ChayaninNapia/IoT_SmartWatt_Meter/proposal/G03_ใบเปิดโครงการ.pdf

โครงงานศึกษา Class Project สถาบันวิทยาการหุ่นยนต์ภาคสนาม (ฟีโบ้) มหาวิทยาลัยเทคโนโลยีพระจอมเกล้าธนบุรี ประจําปีการศึกษา 2/2569

วิชาเรียน
วิชา FRA 163 สตูดิโอวิทยาการหุ่นยนต์ 1 : ขับเคลื่อนด้วยวิทยาศาสตร์ (Robotics Studio I : Science in Motion) ชื่อโครงงาน
เครื่องยิงลูกสควอสแบบปริงกด

ผู้รับผิดชอบโครงงาน
นักศึกษาระดับปริญญาตรี ชั้นปีที่ 1 (รหัส 68) จํานวน 6 คน กลุ่มที่ 3
1. นายชวัลกร | ฐานพงศ์พันธุ์ | รหัสนักศึกษา 68340500016
2. นายโชติพิสุทธิ์ มงคลวิสุทธิ์ | รหัสนักศึกษา 68340500020
3. นางสาวพีรยา กันสิงห์ | รหัสนักศึกษา 68340500042
4. นายพีรวิชญ์ | ศิริเศรษฐ์ | รหัสนักศึกษา 68340500043
5. นายจิรวัฒน์ | ดอนโบราณ | รหัสนักศึกษา 68340500060
6. นายมณฑล | จวงสันเทียะ | รหัสนักศึกษา 68340500078

อาจารย์ที่ปรึกษากลุ่ม
1. ผศ.ดร.เอกชัย เป็งวัง
2. ดร.รัตนชัย รมัยธิติมา
3. ดร.บุญฑริกา เกษมสันติธรรม
4. ดร.ปิติวุฒญ์ ธีรกิตติกุล
5. ดร.วุฒิพงษ์ ปรีชาพลกุล
6. นายพุฒินาท อาชีวะวานิช
บทนํา
เครื่องยิงลูกสควอชที่ใช้กลไกสปริงกดในการส่งกําลังและยิงลูกสควอชออกไปตกในเป้าหมายที่กําหนดไว้ โดยหลักการ ทํางานของเครื่องคือการใช้ Linear Guide เคลื่อนที่เพื่อให้Solenoid Lock เข้าหากัน และใช้ Lead Screw ในการดึงให้ Solenoid Lock ลงมาจนถึงระยะที่กําหนดไว้ ทําการหน่วงเวลาด้วยวงจรไฟฟ้า Timer Circuit เมื่อถึงเวลาที่กําหนดไว้Solenoid Lock จะปล่อยออกจากกัน จึงทําให้ลูกสควอชถูกยิงออกไป

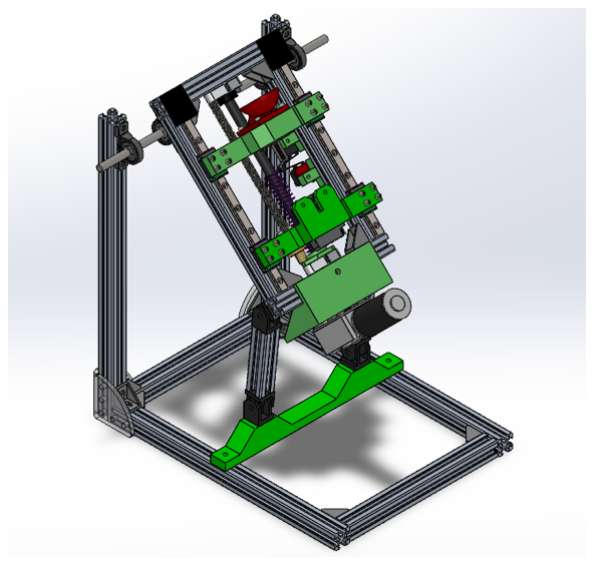
[picture p4: figure]

ขอบเขตของโครงงาน
1. ลูกบอลที่ใช้ในการทดสอบ และแข่งขันเป็นลูกสควอชตามมาตรฐาน (Standard Squash Ball: 1 Yellow dot)
2. กําหนดให้แต่ละทีมยิงลูกสควอชเข้าห่วงที่วางบนฐานหมุน โดยที่ปากห่วงมีขนาดเส้นผ่าศูนย์กลาง120 mm. และตั้งอยู่ในแนว ระนาบขนานกับพื้น โดยมีระยะจากปลายกระบอกเครื่องยิงและจุดศูนย์กลางฐานหมุนประมาณ 2500 mm.
3. ตําแหน่งของห่วงถูกกําหนดด้วยระยะห่างจากจุดศูนย์กลางของฐานหมุน ซึ่งแกนสําหรับวางฐานหมุนจะมีความยาวประมาณ 850 mm. และขอบห่วงจะอยู่สูงจากพื้นดินประมาณ 430 mm.
4. ฐานหมุนจะถูกกําหนดให้เคลื่อนที่ด้วยความเร็วเชิงมุมคงที่ตลอดการยิงแต่ละรอบ และจะมีการส่งสัญญาณไปยังเครื่องยิงเมื่อ แกนหลักของฐานวางห่วงเคลื่อนที่ไปยังองศาที่กําหนด
5. ตัวแปรที่เกี่ยวข้องกับเป้าหมายมี 3 ค่าคือตําแหน่งของห่วงจากจุดศูนย์กลางฐานหมุน [mm], ความเร็วเชิงมุมคงที่ของฐาน หมุน [rad/s], และตําแหน่งแกนหมุนที่ฐานหมุนจะส่งสัญญาณไปยังเครื่องยิง [rad]
6. ทุกส่วนของเครื่องยิงต้องวางบนพื้น และอยู่ภายในพื้นที่ที่กําหนดทุกช่วงขณะของการเคลื่อนที่ และเครื่องยิงต้องมีขนาดความ สูงไม่เกิน 500 mm.
7. ภายในห่วงจะมีการใส่ตาข่ายเพื่อช่วยให้ลูกสควอชหยุดได้ง่ายขึ้น การยิงแต่ละครั้งจะนับคะแนนก็ต่อเมื่อลูกสควอชเคลื่อนที่ เข้าห่วงและหยุดอยู่ภายในตาข่ายเท่านั้น
8. เครื่องยิงควรมีขนาด และนํ้าหนักที่เหมาะแก่การเคลื่อนย้าย โดยนํ้าหนักไม่ควรเกิน 4 กก.
9. โปรแกรมจําลองการเคลื่อนที่ต้องสามารถคํานวณหาค่าพารามิเตอร์ของการยิง เมื่อเป้าหมายและสภาพแวดล้อมเปลี่ยนแปลง ไป พร้อมการแสดงวิถีการยิงหรือแสดงค่าพารามิเตอร์อื่นที่จะปรับตามและมีส่วนติดต่อกับผู้ใช้งานอย่างเหมาะสม
10. เมื่อลูกถูกวางลงบนตัวเครื่องแล้ว และระบบได้รับคําสั่งเริ่มการทํางานโดยผู้ควบคุมได้เพียงครั้งเดียวซึ่งสามารถใช้การกดสวิตช์ หลังจากนั้นเครื่องยิงจะต้องทํางานแบบอัตโนมัติจนลูกออกจากตัวเครื่องยิง และกลับมาที่จุดตั้งต้น (Home) เตรียมรับการ ป้อนลูก (feed) ต่อไป
11. สามารถใช้สัญญาณระบุตําแหน่งเชิงมุมจากฐานหมุนเพื่อเพิ่มความแม่นยําในการยิงแต่ละครั้งได้
12. ขั้นตอนการป้อนลูกไม่จําเป็นต้องอัตโนมัติ
13. การทํางานอัตโนมัติทั้งหมดใช้การสั่งงานควบคุมจากวงจรไฟฟ้าอิเล็กทรอนิกส์เท่านั้น
14. การยิงแต่ละครั้งให้ยิงได้แค่ลูกเดียว
15. ในการยิงแต่ละครั้ง จะมีการกําหนดค่าทั้ง 3 ของเป้าหมาย นักศึกษาสามารถจับและปรับตําแหน่งเครื่องยิงได้ก่อนการยิงในแต่ ละครั้ง แต่ต้องอ้างอิงข้อมูลจากโปรแกรมจําลองการเคลื่อนที่ที่ออกแบบมาเท่านั้น
16. เครื่องยิงและอุปกรณ์ที่ใช้ต้องถูกเก็บสายไฟให้เป็นระเบียบเรียบร้อย ไม่ให้ผู้ทดสอบสามารถดึงสายไฟหรือแตะต้อง องค์ประกอบทางไฟฟ้าได้ง่าย
17. โปรแกรมจําลองการเคลื่อนที่ต้องสามารถคํานวณหาค่าพารามิเตอร์ของการยิง เมื่อเป้าหมายและเปลี่ยนแปลงไป พร้อมการ แสดงวิถีการยิงหรือแสดงค่าพารามิเตอร์อื่นที่จะปรับตามและมีส่วนติดต่อกับผู้ใช้งานอย่างเหมาะสม

วัตถุประสงค์ของโครงงาน
1. เพื่อศึกษาวิถีการเคลื่อนที่ของลูกสควอช โดยการคํานวณและทฤษฎีการเคลื่อนที่วิถีโค้ง
2. เพื่อวิเคราะห์ข้อมูลข้อดีข้อเสียของกลไกการยิงแต่ละประเภท
3. เพื่อออกแบบ วางระบบไฟฟ้า ให้เป็นไปตามหลักการทางวิศวกรรม และคํานวณวิถีการเคลื่อนที่ของลูกสควอชด้วยหลักการ ทางวิทยาศาสตร์
4. เพื่อสร้างเครื่องยิงลูกสควอชที่สามารถทําตามเงื่อนไขของรายวิชาได้ตามเป้าหมาย
5. เพื่อเพิ่มทักษะการทํางานและประสานงานร่วมกับผู้อื่น

ประโยชน์ที่คาดว่าจะได้รับ
1. สามารถนําองค์ความรู้จากรายวิชา FRA121, FRA130, FRA131, FRA142 มาบูรณาการและสร้างเป็นเครื่องยิงลูกสควอชได้ ตามเป้าหมาย
2. สามารถนํากระบวนการทางวิทยาศาสตร์มาประยุกต์ใช้กับการทําเครื่องยิงลูกสควอช
3. สามารถวิเคราะห์ เปรียบเทียบเครื่องยิงแต่ละประเภท จากการทดลองกลไกการยิงหลากหลายรูปแบบ

ระยะเวลาและแผนการปฏิบัติงาน
1. โครงงานเริ่มปฎิบัติงานเมื่อ เดือนมกราคม 2569 สิ้นสุดการปฎิบัติงานเมื่อ เดือนพฤษภาคม 2569
2. ขั้นตอนการดําเนินงานและแผนปฎิบัติงาน
การดําเนินงาน | ระยะเวลา
มกราคม | กุมภาพันธ์ | มีนาคม | เมษายน | พฤษภาคม
1 | 2 | 3 | 4 | 1 | 2 | 3 | 4 | 1 | 2 | 3 | 4 | 1 | 2 | 3 | 4 | 1 | 2 | 3 | 4
Milestone 0
ศึกษาทฤษฎีที่เกี่ยวกับการ เคลื่อนที่ของลูกสควอช

ออกแบบ Concept เครื่องยิง ลูกสควอช

ประเมินต้นทุนการใช้จ่ายในการ ทําเครื่องยิงลูกสควอช

ทดลอง Simulation ใน MATLAB และ Unreal Engine

นําเสนอ Milestone 0 เพื่อรับ Feedback และนํามาแก้ไข

Milestone 1
CAD ตาม Concept ที่ ออกแบบไว้

ปรับปรุง CAD และทํา Ball of material (BOM)

ออกแบบวงจรควบคุมและออก อุปกรณ์การจ่ายไฟ

การทดลองที่ 1: หาค่าของ K ที่ เหมาะสมกับการยิงของเครื่อง ยิง

จัดหาอุปกรณ์สําหรับทําการ ทดลอง

สรุปแนวทางการทํางานของ เครื่องยิงลูกสควอช

การทดลองที่ 2 : หามุมที่ สัมพันธ์แรงสปริง

การคัดเลือกใช้วัสดุและประเมิน ต้นทุนในการสร้างเครื่องยิง

จัดทํารูปเล่มรายงาน M1 และ Presentation

นําเสนอ Milestone 1 และนํา Feedback ไปปรับปรุง

Milestone 2
จัดทํารูปเล่มรายงาน Milestone 2 และ Presentation

นําเสนอ M2 และรับ Feedback เพื่อนํากลับไปแก้ไข

Milestone 3
CAD ขึ้นรูปชิ้นส่วนของเครื่อง ยิง

ประกอบเครื่องยิง
ทดสอบเครื่องยิงและปรับปรุง ประสิทธิภาพเครื่องยิง

ทํารายการรายรับ -รายจ่ายใน การทําเครื่องยิง

จัดทํารูปเล่มรายงานและ Presentation

นําเสนอ Milestone 3

งบประมาณ
ลําดับ | รายละเอียด | จํานวน | จํานวนเงิน (บาท) | หมายเหตุ | แหล่งที่มา
1 | Linear rail MGN9 200mm | 2 | 528 | | urlkub.co/fCwO9k
2 | Linear block MGN9C | 4 | 1008 | | urlkub.co/D3oBwP
3 | Solenoid lock 12V 1.4A | 2 | 256 | | urlkub.co/CZiILt
4 | Vertical Pillow bearing 8mm | 6 | 198 | | urlkub.co/efqCb6
5 | Leadscrew set 8mm L:200mm | 1 | 149 | | urlkub.co/h2YGio
6 | Wormgear motor 12V | 1 | 703 | | urlkub.co/KUZU2K
7 | Spring Misumi K3360 | 1 | 257 | | urlkub.co/x4YXFw
8 | Shaft 10mm L:200m | 1 | 90 | | urlkub.co/1Wmem5
9 | Aluminum profile 70cm | 1 | 212 | | urlkub.co/LbsBnP
10 | Limit switch | 4 | 140 | | urlkub.co/9GZjdd
11 | Filament PETG 1kg | 1 | 399 | | urlkub.co/BOoCXF
12 | IC555 NE555 NE555P DIP-8 | 10 | 40 | | urlkub.co/Nu5Snp
13 | Mosfet IRFZ44N 49A 55V | 5 | 100 | | urlkub.co/nOzZAp
14 | Capacitor 100uF 25V 6x12 | 9 | 9 | | urlkub.co/CWH0ml
15 | CeramicCapacitor10350V0.01UF7ชิ้น | 2 | 14 | | urlkub.co/Ib6pKH
16 | 1N4148 Diode 1N4148 | 10 | 15 | | urlkub.co/53dMOe
17 | 1N4007 Diode 1N4007 1A 1000V Rectifier Diode 5 ชิ้น | 4 | 12 | | urlkub.co/NNe5HV
18 | Resistor 150kΩ 1/4W 1% | 20 | 20 | | urlkub.co/4jzdTf
19 | Resistor 10kΩ 1/4W 5% | 1 | 30 | | urlkub.co/zKHj2l
20 | 220/24VAC 5A TRANSFORMER INPUT220VAC OUTPUT 24VAC 5A | 1 | 679 | | urlkub.co/Go953C
21 | IC PC817 Opto Isolator DIP-4 High Density transistor | 5 | 25 | | urlkub.co/G6JU9f
22 | Capacitor 4700uF 50V | 3 | 51 | | urlkub.co/ucLHKQ
23 | 10A 1000V BRIDGE RECTIFIER | 4 | 52 | | urlkub.co/zsm9Jm
24 | Step down LM2596 | 2 | 44 | | urlkub.co/CHyF61
25 | IC 7812 Regulator 12V 1.5A | 3 | 27 | | urlkub.co/zZN7dt
26 | Fuse 5A 250V | 2 | 6 | | urlkub.co/APQYNE
27 | Mosfet IC Heatsink 17x20x7 | 1 | 36 | | urlkub.co/OqIBbZ
28 | Free Angle Bracket 20 | 4 | 900 | | urlkub.co/b4NZH2
| รวมเป็นเงิน | | 6,000
หมายเหตุ : ขอถัวเฉลี่ยค่าใช้จ่ายทุกรายการ
ลงชื่อ | อาจารย์ที่ปรึกษา
