ChayaninNapia/IoT_SmartWatt_Meter/draft/fra_503_project_requirements.md

# FRA503 IoT

จำนวนสมาชิก 1-3 คน โดยขอบเขตงานจะปรับตามจำนวนสมาชิก

## Proposal Content

Introduction, objective, scope, background study, work plan\
(Methodology ใน final report), budget plan

- Problem/Solution Fit สามารถแสดงให้เห็นถึงโจทย์ที่มีอยู่ (ไม่จำเป็นต้องแสดงว่ามีความต้องการมาก หรือน้อย จะเป็นโจทย์เฉพาะของตนเองก็ได้ แต่ต้องสามารถอธิบายให้เห็นความต้องการได้ชัดเจน กระชับ) แล้วเสนอวิธี/ไอเดียการแก้ปัญหา อธิบาย features ทั้งหมดที่คิดว่า solution ควรต้องมี
- ขอบเขตงาน จาก solution ที่เสนอมา เราควรอธิบายว่าจะทำครอบคลุม features/องค์ประกอบไหนบ้าง เพราะอะไร
- ศึกษา alternative solutions มีให้เห็นเป็นตัวอย่าง 1-3 products/services
- Technical Feasibility (ความเป็นไปได้เชิงเทคนิคในการทำโปรเจ็ค หาข้อมูลให้ได้มากที่สุด ถึงแนวทางการดำเนินงาน
- แผนการดำเนินงาน
- งบการดำเนินงาน

## Project Description

เป็นระบบ IoT ที่ประกอบด้วย ส่วนต่อไปนี้

- Devices อย่างน้อย 2 ตัว + Communication + Security หากเป็นกลุ่ม 3 คนต้องมี Application ด้วย โดย

- device นั้นจะต้องมีตัวหนึ่งเป็นตัวตรวจจับ และทำการตรวจจับ หลังส่งผลการสั่งการทำงานของอีกตัว (actuate another device) ได้ โดยการสั่งการทำงานอาจจะเป็นแบบอัตโนมัติหรือไม่ก็ได้\
  devices นั้นเป็นการพัฒนาขึ้นเอง หรือเป็นการเลือกใช้ก็ได้ โดยจะต้องแสดงให้เห็น วิธีการพัฒนา และ/หรือ กระบวนการ setting, config ในรายงาน

- เป็นโจทย์ที่มีความต้องการจริง (proposal)

- ทำการศึกษา และวิเคราะห์ระบบที่มีอยู่แล้ว (proposal)

- มีการสื่อสารกันในระบบ IoT นี้

- ระบบ prototype มีความสมบูรณ์ในระดับทดสอบการใช้งานได้ โดยต้องผ่านการทดสอบการใช้งานก่อนจะหยิบถ่ายนำเสนอสรุปสุดท้าย

- มีความฉลาด อาจเป็นระบบตัดสินใจแบบอัตโนมัติแบบ rule base ที่มี parameters มากกว่า 1 ตัว, เป็นระบบตัดสินใจบนพื้นฐานของข้อมูลตรวจจับแบบไม่อัตโนมัติ แต่เป็นแอปให้คนเลือกตัดสินใจ โดยการวิเคราะห์ข้อมูลที่ใช้สนับสนุนการตัดสินใจนั้นไม่ใช่แค่ rule base

- เป็นระบบตัดสินแบบอัตโนมัติ โดยข้อมูลที่ใช้ประกอบการตัดสินใจนั้นจะต้องผ่านกระบวนการที่มากกว่า rule base

## Extra Credits

- มีการเรียกใช้ services (จะเป็นที่เขียนขึ้นเอง หรือ services จากการให้บริการต่าง ๆ ก็ได้)
- พัฒนาระบบได้เร็วระดับพร้อมขาย เช่น การ setup ที่ง่าย (ขึ้นอยู่กับ business model เช่นถ้าเป็นอุปกรณ์ IoT ที่ขายขาดเป็นอุปกรณ์ prototype ที่สร้างขึ้นนี้ก็ควรจะพัฒนาการควบคุมช่วง setting/config โดยผู้ใช้ด้วย)

คะแนนกลุ่มจะคิดด้วย Contribution Weight (CW) โดยจะเป็นการให้น้ำหนักในมิติของการทำงานร่วมกัน

1. เรื่องความตรงต่อเวลาในการส่งงานกลุ่ม
2. คุณภาพงานในส่วนที่ตนเองรับผิดชอบ\
   อื่น ๆ ในมิติที่สมาชิกในกลุ่มเห็นตรงกันว่าควรจะให้คะแนนด้วย

## Phase I: Proposal Submission and Presentation

1. ส่งไฟล์ตามกำหนดเวลาในกล่องรับการบ้าน MS Team และตั้งชื่อไฟล์ตาม template ต่อไปนี้\
   (FRA503 Project Proposal Report YY### ....) โดยตัวเอียง Report ถ้าเป็นไฟล์นำเสนอให้เปลี่ยนเป็น Present และ YY แทนด้วยเลข 2 ตัวแรกของรหัสนิสิต และ ### แทนด้วยเลข 3 ตัวหลังของรหัสนิสิต\
   1.1 ไฟล์เอกสาร โดยมี format ตามโครงร่างปกติ ประกอบด้วยเนื้อหาทั่วไป และเนื้อหาในหัวข้อด้านล่าง\
   1.2 ไฟล์นำเสนอ
2. Purpose & Requirements Specifications: กำหนดโจทย์ วัตถุประสงค์ ขอบเขต และผลลัพธ์ function ที่ระบบ iot ต้องทำได้ (deliver) อย่างชัดเจน
3. Conceptual Design & System Overview
4. แผนการดำเนินงาน (บรรยายวิธี, gantt chart) การตัดแบ่งภาระงานภายในกลุ่ม
5. แผนงบประมาณ
6. Process Specifications นำเสนอ แสดงให้เห็นถึงกระบวนการทางการทำงานหรือการคิดของระบบ ในรูปแบบที่ผู้ที่ไม่รู้ด้านนี้ก็เข้าใจง่าย
7. Domain Specification ระบุ แสดงอธิบาย ความเกี่ยวโยงขององค์ประกอบต่าง ๆ ระหว่าง Domains เหล่านี้ได้ physical Domain, virtual Domain, resources, services และ devices ของระบบได้
8. ระบบและอธิบายองค์ประกอบต่าง ๆ ในระบบ iot นี้ที่มีมาเข้ามาด้วย อาจอ้างอิงจาก diagram ในเอกสารสื่อสารง่าย
9. แสดง และอธิบายวิธีการทดลอง การทดสอบต่าง ๆ ที่เกี่ยวข้องในโครงงานได้
10. วิเคราะห์ และสรุป ผลการทดลอง/ทดสอบต่าง ๆ รวมไปถึงผลลัพธ์สุดท้ายของระบบได้

---

หมายเหตุ: ข้อความนี้ถอดมาจาก PDF ต้นฉบับที่เป็นภาพสแกน อาจมีบางจุดคลาดเคลื่อนเล็กน้อยจากต้นฉบับ
