ChayaninNapia/IoT_SmartWatt_Meter/data/hx711_calibration/loading/m0/trial03/hx711_capture.csv

sample_idx | time_ms | raw | delta_raw | zero_raw
1 | 532636 | 237382 | -5206 | 242588
2 | 532700 | 237349 | -5239 | 242588
3 | 532790 | 237353 | -5235 | 242588
4 | 532879 | 237346 | -5242 | 242588
5 | 532969 | 237296 | -5292 | 242588
6 | 533058 | 237288 | -5300 | 242588
7 | 533148 | 237284 | -5304 | 242588
8 | 533238 | 237259 | -5329 | 242588
9 | 533327 | 237291 | -5297 | 242588
10 | 533417 | 237315 | -5273 | 242588
11 | 533507 | 237329 | -5259 | 242588
12 | 533596 | 237312 | -5276 | 242588
13 | 533686 | 237277 | -5311 | 242588
14 | 533776 | 237287 | -5301 | 242588
15 | 533865 | 237279 | -5309 | 242588
16 | 533955 | 237225 | -5363 | 242588
17 | 534045 | 237193 | -5395 | 242588
18 | 534134 | 237140 | -5448 | 242588
19 | 534224 | 237101 | -5487 | 242588
20 | 534314 | 237109 | -5479 | 242588
21 | 534403 | 237091 | -5497 | 242588
22 | 534493 | 237048 | -5540 | 242588
23 | 534583 | 237046 | -5542 | 242588
24 | 534672 | 237019 | -5569 | 242588
25 | 534762 | 237037 | -5551 | 242588
26 | 534852 | 237051 | -5537 | 242588
27 | 534941 | 237045 | -5543 | 242588
28 | 535031 | 237009 | -5579 | 242588
29 | 535120 | 236975 | -5613 | 242588
30 | 535210 | 236969 | -5619 | 242588
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
