ChayaninNapia/IoT_SmartWatt_Meter/data/hx711_calibration/loading/m1/trial01/hx711_capture.csv

sample_idx | time_ms | raw | delta_raw | zero_raw
1 | 210857 | 249764 | 7176 | 242588
2 | 210933 | 249784 | 7196 | 242588
3 | 211023 | 249804 | 7216 | 242588
4 | 211113 | 249780 | 7192 | 242588
5 | 211202 | 249784 | 7196 | 242588
6 | 211292 | 249732 | 7144 | 242588
7 | 211382 | 249701 | 7113 | 242588
8 | 211471 | 249662 | 7074 | 242588
9 | 211561 | 249592 | 7004 | 242588
10 | 211651 | 249505 | 6917 | 242588
11 | 211740 | 249473 | 6885 | 242588
12 | 211830 | 249474 | 6886 | 242588
13 | 211919 | 249470 | 6882 | 242588
14 | 212009 | 249466 | 6878 | 242588
15 | 212099 | 249494 | 6906 | 242588
16 | 212188 | 249497 | 6909 | 242588
17 | 212278 | 249502 | 6914 | 242588
18 | 212368 | 249548 | 6960 | 242588
19 | 212457 | 249549 | 6961 | 242588
20 | 212547 | 249578 | 6990 | 242588
21 | 212637 | 249604 | 7016 | 242588
22 | 212726 | 249676 | 7088 | 242588
23 | 212816 | 249719 | 7131 | 242588
24 | 212906 | 249740 | 7152 | 242588
25 | 212995 | 249753 | 7165 | 242588
26 | 213085 | 249815 | 7227 | 242588
27 | 213175 | 249799 | 7211 | 242588
28 | 213264 | 249843 | 7255 | 242588
29 | 213354 | 249858 | 7270 | 242588
30 | 213444 | 249838 | 7250 | 242588
31 | 213533 | 249844 | 7256 | 242588
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
