ChayaninNapia/IoT_SmartWatt_Meter/data/hx711_calibration/loading/m1/trial02/hx711_capture.csv

sample_idx | time_ms | raw | delta_raw | zero_raw
1 | 429366 | 247336 | 4748 | 242588
2 | 429419 | 247331 | 4743 | 242588
3 | 429508 | 247319 | 4731 | 242588
4 | 429598 | 247260 | 4672 | 242588
5 | 429688 | 247296 | 4708 | 242588
6 | 429777 | 247282 | 4694 | 242588
7 | 429867 | 247239 | 4651 | 242588
8 | 429956 | 247234 | 4646 | 242588
9 | 430046 | 247202 | 4614 | 242588
10 | 430136 | 247157 | 4569 | 242588
11 | 430225 | 247152 | 4564 | 242588
12 | 430315 | 247189 | 4601 | 242588
13 | 430405 | 247203 | 4615 | 242588
14 | 430494 | 247172 | 4584 | 242588
15 | 430584 | 247187 | 4599 | 242588
16 | 430674 | 247168 | 4580 | 242588
17 | 430763 | 247198 | 4610 | 242588
18 | 430853 | 247214 | 4626 | 242588
19 | 430943 | 247218 | 4630 | 242588
20 | 431032 | 247208 | 4620 | 242588
21 | 431122 | 247236 | 4648 | 242588
22 | 431212 | 247269 | 4681 | 242588
23 | 431301 | 247288 | 4700 | 242588
24 | 431391 | 247294 | 4706 | 242588
25 | 431481 | 247291 | 4703 | 242588
26 | 431570 | 247314 | 4726 | 242588
27 | 431660 | 247296 | 4708 | 242588
28 | 431750 | 247285 | 4697 | 242588
29 | 431839 | 247316 | 4728 | 242588
30 | 431929 | 247349 | 4761 | 242588
31 | 432019 | 247343 | 4755 | 242588
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
