ChayaninNapia/IoT_SmartWatt_Meter/data/hx711_calibration/loading/m1/trial03/hx711_capture.csv

sample_idx | time_ms | raw | delta_raw | zero_raw
1 | 559915 | 247759 | 5171 | 242588
2 | 559955 | 247752 | 5164 | 242588
3 | 560044 | 247746 | 5158 | 242588
4 | 560134 | 247715 | 5127 | 242588
5 | 560224 | 247732 | 5144 | 242588
6 | 560313 | 247751 | 5163 | 242588
7 | 560403 | 247773 | 5185 | 242588
8 | 560493 | 247812 | 5224 | 242588
9 | 560582 | 247789 | 5201 | 242588
10 | 560672 | 247754 | 5166 | 242588
11 | 560762 | 247805 | 5217 | 242588
12 | 560851 | 247799 | 5211 | 242588
13 | 560941 | 247814 | 5226 | 242588
14 | 561031 | 247816 | 5228 | 242588
15 | 561120 | 247848 | 5260 | 242588
16 | 561210 | 247894 | 5306 | 242588
17 | 561300 | 247964 | 5376 | 242588
18 | 561389 | 247945 | 5357 | 242588
19 | 561479 | 247993 | 5405 | 242588
20 | 561569 | 248002 | 5414 | 242588
21 | 561658 | 247967 | 5379 | 242588
22 | 561748 | 247919 | 5331 | 242588
23 | 561838 | 247910 | 5322 | 242588
24 | 561927 | 247892 | 5304 | 242588
25 | 562017 | 247886 | 5298 | 242588
26 | 562106 | 247847 | 5259 | 242588
27 | 562196 | 247845 | 5257 | 242588
28 | 562286 | 247862 | 5274 | 242588
29 | 562375 | 247820 | 5232 | 242588
30 | 562465 | 247844 | 5256 | 242588
31 | 562555 | 247883 | 5295 | 242588
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
